AmirKaseb/Mini-Smart-Home-System/Final Report & Deliverables/Hardware/Altium - Shc & PCB Pictures/PCB-Top..png

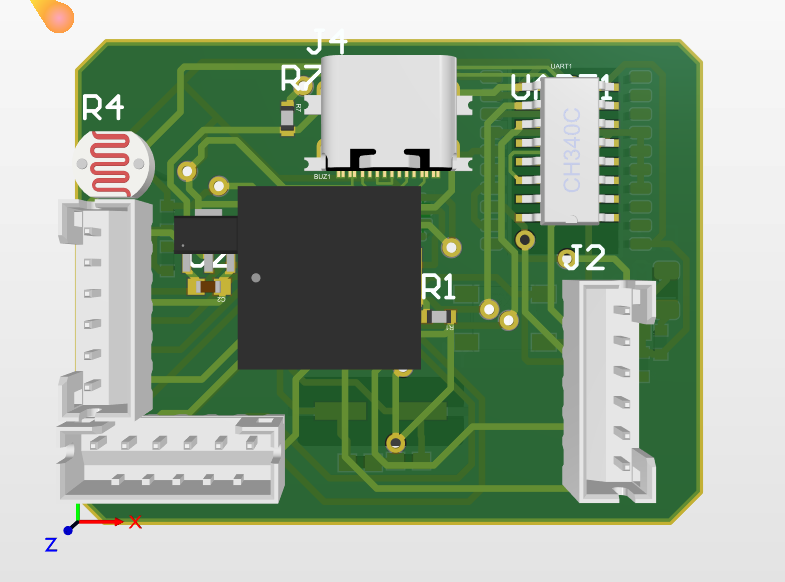
Final Report & Deliverables/Hardware/Altium - Shc & PCB Pictures/PCB-Top..png
